rgeyer/MapADroid/resources/ATVRackSTLs/PSUBracket.stl

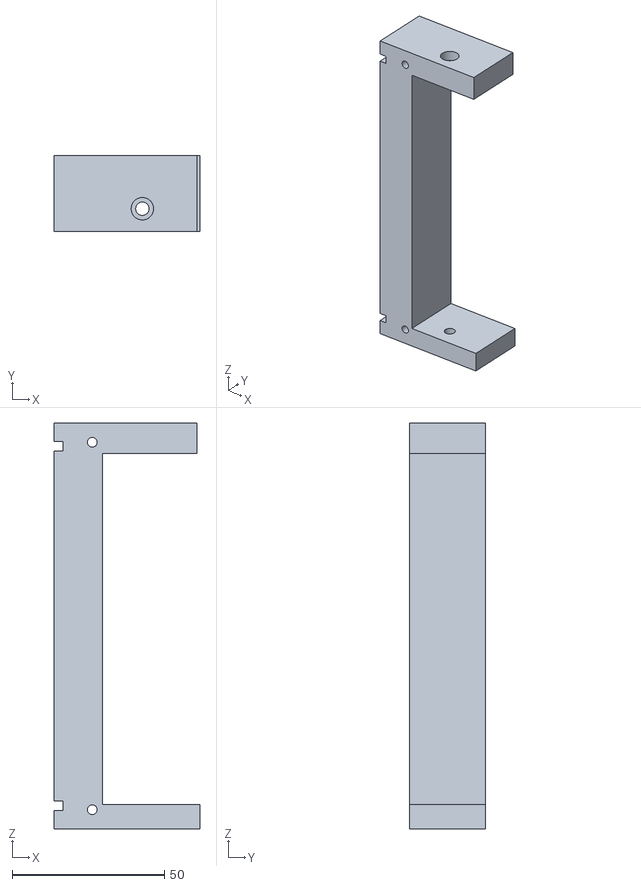
[picture p15: CAD file, 2020-03-10]
resources/ATVRackSTLs/PSUBracket.stl
47.9 x 25.0 x 133.4
