rgeyer/MapADroid/resources/ATVRackSTLs/Tray.stl

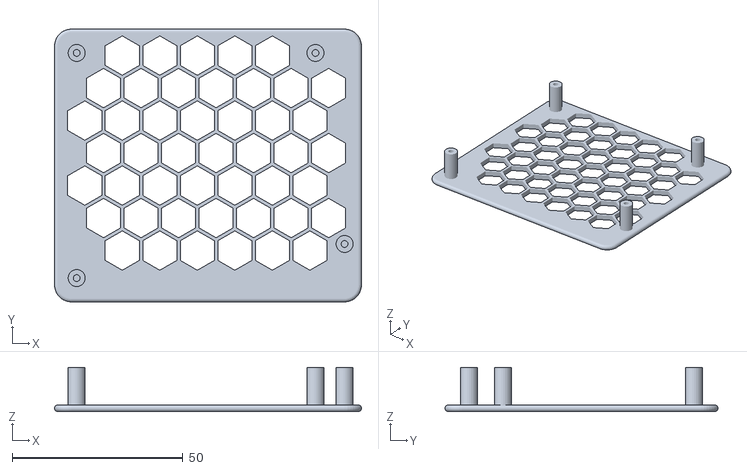
[picture p16: CAD file, 2020-03-10]
resources/ATVRackSTLs/Tray.stl
90.0 x 80.0 x 13.0
