rgeyer/MapADroid/resources/ATVRackSTLs/ATVRearLidTop.stl

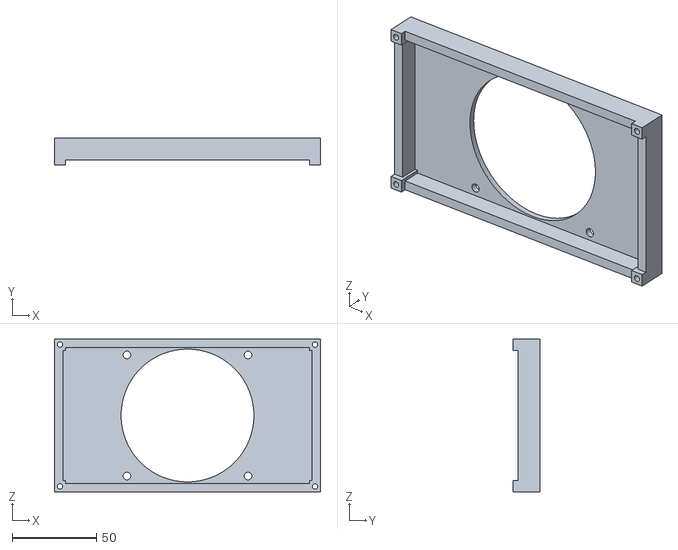
[picture p17: CAD file, 2020-03-10]
resources/ATVRackSTLs/ATVRearLidTop.stl
158.2 x 16.0 x 90.8
