rgeyer/MapADroid/src/eagle/madrack.sch

## EAGLE design src/eagle/madrack.sch (2020-03-10)

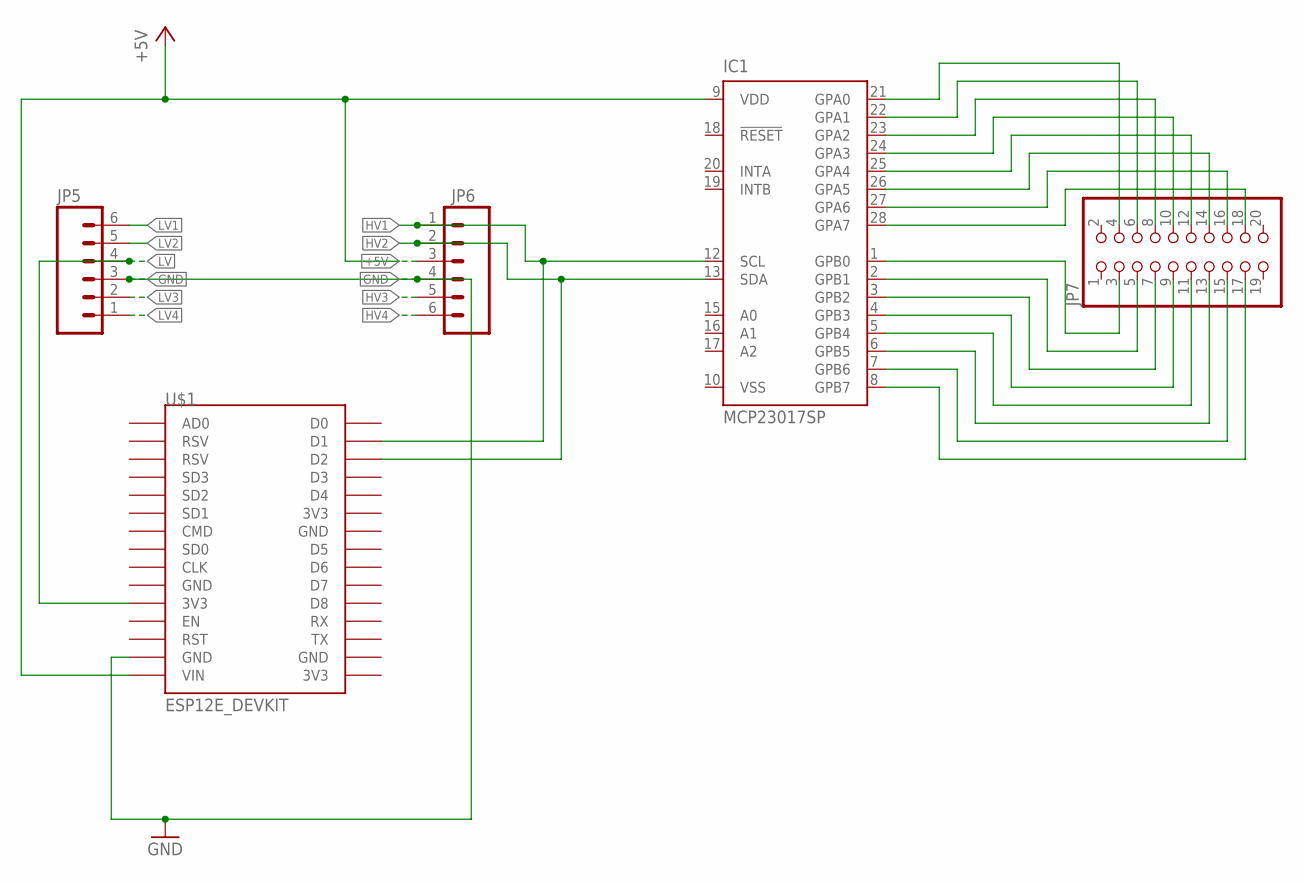
[picture p18: schematic madrack.sch]

Parts:
IC1: MCP23017SP; DIL28-3
JP5, JP6: M06SIP; 1X06
JP7: PINHD-2X10; 2X10
U$1: ESP12E_DEVKIT

Connections:
+5V: IC1.9 (VDD), JP6.3, U$1.VIN
GND: JP5.3, JP6.4, U$1.GND@1 (GND)
HV1: IC1.12 (SCL), JP6.1, U$1.D1
HV2: IC1.13 (SDA), JP6.2, U$1.D2
HV3: JP6.5
HV4: JP6.6
LV: JP5.4, U$1.3V3@0 (3V3)
LV1: JP5.6
LV2: JP5.5
LV3: JP5.2
LV4: JP5.1
unnamed: IC1.28 (GPA7), JP7.18
unnamed: IC1.27 (GPA6), JP7.16
unnamed: IC1.26 (GPA5), JP7.14
unnamed: IC1.25 (GPA4), JP7.12
unnamed: IC1.24 (GPA3), JP7.10
unnamed: IC1.23 (GPA2), JP7.8
unnamed: IC1.22 (GPA1), JP7.6
unnamed: IC1.21 (GPA0), JP7.4
unnamed: IC1.1 (GPB0), JP7.3
unnamed: IC1.2 (GPB1), JP7.5
unnamed: IC1.3 (GPB2), JP7.7
unnamed: IC1.4 (GPB3), JP7.9
unnamed: IC1.5 (GPB4), JP7.11
unnamed: IC1.6 (GPB5), JP7.13
unnamed: IC1.7 (GPB6), JP7.15
unnamed: IC1.8 (GPB7), JP7.17
