rgeyer/MapADroid/src/platformio/src/relays.h

# include <Arduino.h>

const uint16_t RELAY1=32768; // BIT 16
const uint16_t RELAY2=1; // BIT 1
const uint16_t RELAY3=16384; // BIT 15
const uint16_t RELAY4=2; // BIT 2
const uint16_t RELAY5=8192; // BIT 14
const uint16_t RELAY6=4; // BIT 3
const uint16_t RELAY7=4096; // BIT 13
const uint16_t RELAY8=8; // BIT 4
const uint16_t RELAY9=2048; // BIT 12
const uint16_t RELAY10=16; // BIT 5
const uint16_t RELAY11=1024; // BIT 11
const uint16_t RELAY12=32; // BIT 6
const uint16_t RELAY13=512; // BIT 10
const uint16_t RELAY14=64; // BIT 7
const uint16_t RELAY15=256; // BIT 9
const uint16_t RELAY16=128; // BIT 8
